Flynsky/MillerProject/doc/ArbeitsAufteilung.png

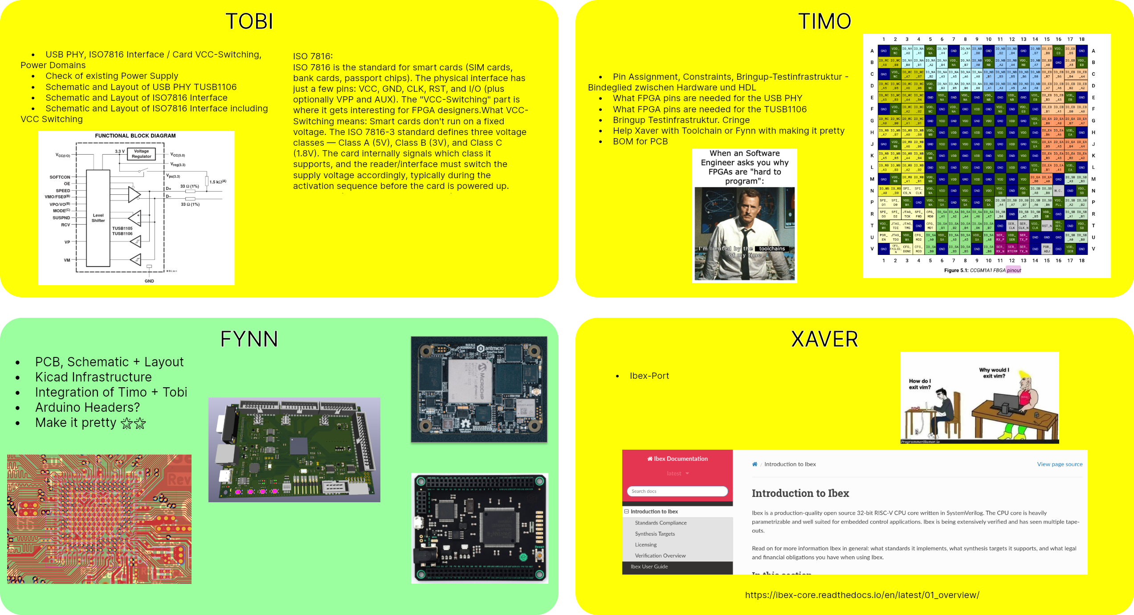
doc/ArbeitsAufteilung.png
