Flynsky/MillerProject/doc/reports/assets/render_no_comp.png

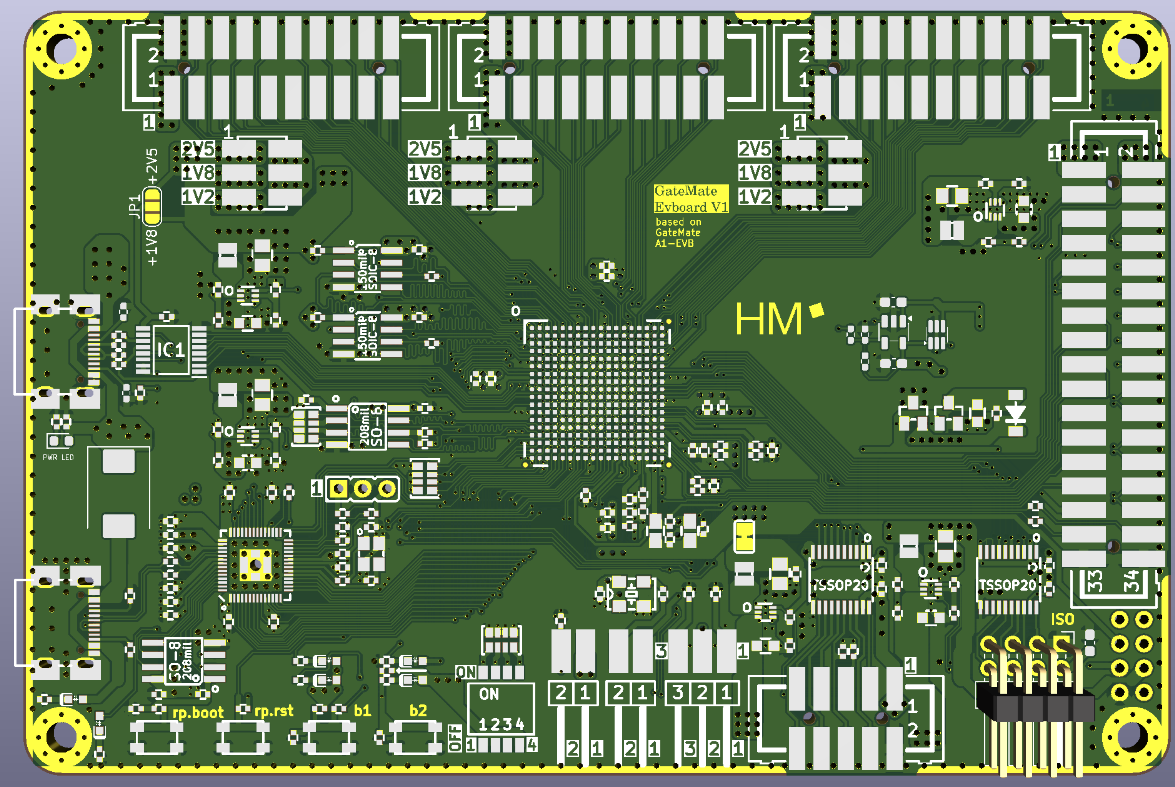
doc/reports/assets/render_no_comp.png
