Flynsky/MillerProject/doc/reports/assets/renderISO.png

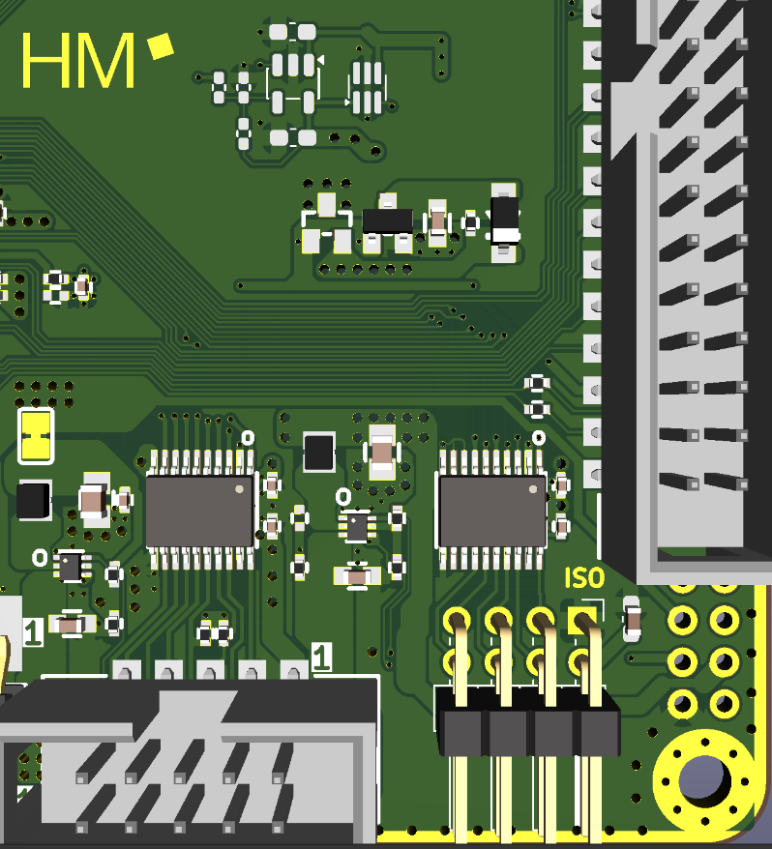
doc/reports/assets/renderISO.png
