Flynsky/MillerProject/doc/reports/assets/stackup.png

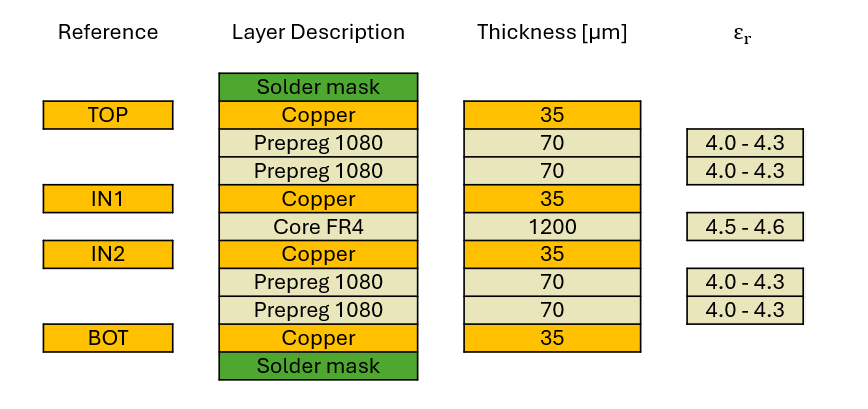
doc/reports/assets/stackup.png
