Flynsky/MillerProject/software/sys_verilog_test/schematic.png

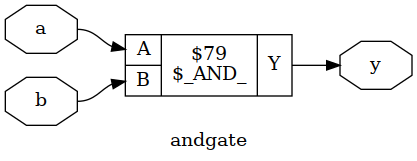
software/sys_verilog_test/schematic.png
