Flynsky/MillerProject/they-have-played-us-for-absolute-fools-v0-pewh6yrhfmp91.webp

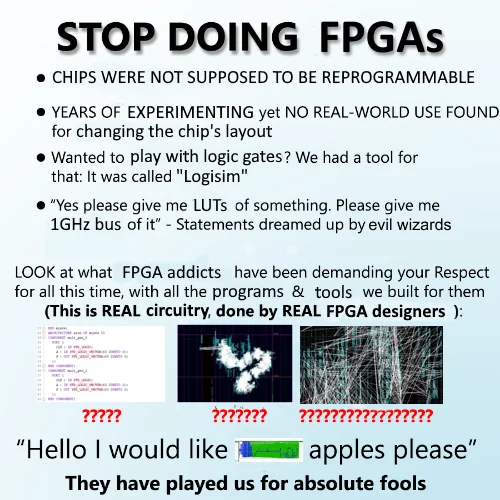
they-have-played-us-for-absolute-fools-v0-pewh6yrhfmp91.webp
